bobbycar-reinvented/bobbycar-hardware-remote-v2/firmware/main/typesafeenumchangemenu.h

#pragma once

// 3rdparty lib includes
#include <actions/dummyaction.h>
#include <actions/popscreenaction.h>
#include <actions/pushscreenaction.h>
#include <configwrapper.h>
#include <fmt/core.h>
#include <icons/back.h>

// local includes
#include "bobbyerrorhandler.h"
#include "bobbymenudisplay.h"
#include "bobbytypesafeenum.h"
#include "settings.h"

namespace typesafeenumchangemenu {
    constexpr char TEXT_BACK[] = "Back";

    template<typename TEnum>
    class TypesafeEnumCurrentValueMenuItem :
            public espgui::MenuItem
    {
    public:
        TypesafeEnumCurrentValueMenuItem(ConfigWrapper<TEnum>* config) : m_config{config} {}
        std::string text() const override
        {
            return toString(m_config->value());
        }
        void triggered() override {}

        int color() const override
        {
            return TFT_DARKGREY;
        }
    private:
        ConfigWrapper<TEnum>* m_config;
    };

    template<typename TEnum>
    class TypesafeEnumSetterMenuItem :
            public espgui::MenuItem
    {
    public:
        TypesafeEnumSetterMenuItem(TEnum value, ConfigWrapper<TEnum>* config) : m_value{value}, m_config{config} {}

        std::string text() const override
        {
            return toString(m_value);
        }

        void triggered() override
        {
            if (auto result = m_config->write(configs.nvs_handle_user, m_value); !result)
                BobbyErrorHandler{}.errorOccurred(std::move(result).error());
        }
    private:
        const TEnum m_value;
        ConfigWrapper<TEnum>* m_config;
    };

    template<typename TEnum>
    class TypeSafeChangeMenu :
            public BobbyMenuDisplay
    {
    public:
        TypeSafeChangeMenu(ConfigWrapper<TEnum>* config) : m_config{config}
        {
            using namespace espgui;
            using namespace typesafeenumchangemenu;
            constructMenuItem<TypesafeEnumCurrentValueMenuItem<TEnum>>(m_config);
            constructMenuItem<makeComponent<MenuItem, EmptyText, DummyAction>>();
            iterateEnum<TEnum>::iterate([&](TEnum enum_value, const auto &string_value){
                constructMenuItem<TypesafeEnumSetterMenuItem<TEnum>>(enum_value, m_config);
            });
            constructMenuItem<makeComponent<MenuItem, StaticText<TEXT_BACK>, PopScreenAction, StaticMenuItemIcon<&espgui::icons::back>>>();
        }

        std::string text() const override
        {
            return fmt::format("Select {}", m_config->nvsName());
        }

        void back() override
        {
            espgui::popScreen();
        }
    private:
        ConfigWrapper<TEnum>* m_config;
    };
} // namespace typesafeenumchangemenu

template<typename TEnum, const char *Ttext>
class SwitchScreenTypeSafeChangeMenuItem : public espgui::MenuItem
{
public:
    SwitchScreenTypeSafeChangeMenuItem(ConfigWrapper<TEnum>* config) : m_config{config} {}

    static constexpr const char *STATIC_TEXT = Ttext;
    std::string text() const override
    {
        return Ttext;
    }

    void triggered() override
    {
        espgui::pushScreen<typesafeenumchangemenu::TypeSafeChangeMenu<TEnum>>(m_config);
    }
private:
    ConfigWrapper<TEnum>* m_config;
};

template<typename TEnum, const char *Ttext>
class PopScreenTypeSafeChangeMenuItem : public espgui::MenuItem
{
public:
    PopScreenTypeSafeChangeMenuItem(ConfigWrapper<TEnum>* config) : m_config{config} {}

    static constexpr const char *STATIC_TEXT = Ttext;
    std::string text() const override
    {
        return Ttext;
    }

    void triggered() override
    {
        espgui::popScreen();
    }
private:
    ConfigWrapper<TEnum>* m_config;
};

template<typename TEnum, const char *Ttext>
class PushScreenTypeSafeChangeMenuItem : public espgui::MenuItem
{
public:
    PushScreenTypeSafeChangeMenuItem(ConfigWrapper<TEnum>* config) : m_config{config} {}

    static constexpr const char *STATIC_TEXT = Ttext;
    std::string text() const override
    {
        return Ttext;
    }

    void triggered() override
    {
        espgui::pushScreen<typesafeenumchangemenu::TypeSafeChangeMenu<TEnum>>(m_config);
    }
private:
    ConfigWrapper<TEnum>* m_config;
};
