bobbycar-reinvented/bobbycar-hardware-remote-v2/firmware/main/bobbyerrorhandler.cpp

#include "bobbyerrorhandler.h"

// 3rdparty lib includes
#include <screenmanager.h>

// local includes
#include "screens/bobbypopupscreen.h"

void BobbyErrorHandler::errorOccurred(std::string &&error)
{
    auto newDisplay = std::make_unique<BobbyPopupDisplay>(std::move(error), std::move(espgui::currentDisplay));
    newDisplay->initOverlay();
    espgui::currentDisplay = std::move(newDisplay);
}
