bobbycar-reinvented/bobbycar-hardware-remote-v2/firmware/main/bobbyerrorhandler.h

#pragma once

// 3rdparty lib includes
#include <errorhandlerinterface.h>

struct BobbyErrorHandler : public virtual espgui::ErrorHandlerInterface
{
    void errorOccurred(std::string &&error) override;
};
