bobbycar-reinvented/bobbycar-hardware-remote-v2/firmware/main/bobbymenudisplay.cpp

#include "bobbymenudisplay.h"

// local includes
#include "bobbybuttons.h"

void BobbyMenuDisplay::rawButtonPressed(uint8_t button)
{
    //Base::rawButtonPressed(button);
    if (const auto translated = translateRawButton(button))
        buttonPressed(*translated);
}

void BobbyMenuDisplay::rawButtonReleased(uint8_t button)
{
    //Base::rawButtonReleased(button);
    if (const auto translated = translateRawButton(button))
        buttonReleased(*translated);
}

void BobbyMenuDisplay::buttonPressed(espgui::Button button)
{
    Base::buttonPressed(button);
    buttonPressedCommon(button);
}

void BobbyMenuDisplay::buttonReleased(espgui::Button button)
{
    //Base::buttonReleased(button);
    buttonReleasedCommon(button);
}
