bobbycar-reinvented/bobbycar-hardware-remote-v2/firmware/main/settings.cpp

#include "settings.h"

// 3rdparty lib includes
#include <espwifistack.h>

// local includes
#include "configmanager_priv.h"

std::string defaultHostname()
{
    if (const auto result = wifi_stack::get_default_mac_addr())
        return fmt::format("bobby_{:02x}{:02x}{:02x}", result->at(3), result->at(4), result->at(5));
    else
        ESP_LOGE(TAG, "get_default_mac_addr() failed: %.*s", result.error().size(), result.error().data());
    return "bobby";
}

ConfigManager<ConfigContainer> configs;

INSTANTIATE_CONFIGMANAGER_TEMPLATES(ConfigContainer)
