bobbycar-reinvented/bobbycar-hardware-remote-v2/firmware/main/taskmanager.h

#pragma once

// system includes
#include <optional>

// 3rdparty lib includes
#include <arrayview.h>
#include <schedulertask.h>
#include <tl/expected.hpp>

extern cpputils::ArrayView<espcpputils::SchedulerTask> schedulerTasks;

void sched_pushStats(bool printTasks);
